agam-89/CoreSynq32/schematics/386amp.kicad_sch

## KiCad design schematics/386amp.kicad_sch (2026-04-13)

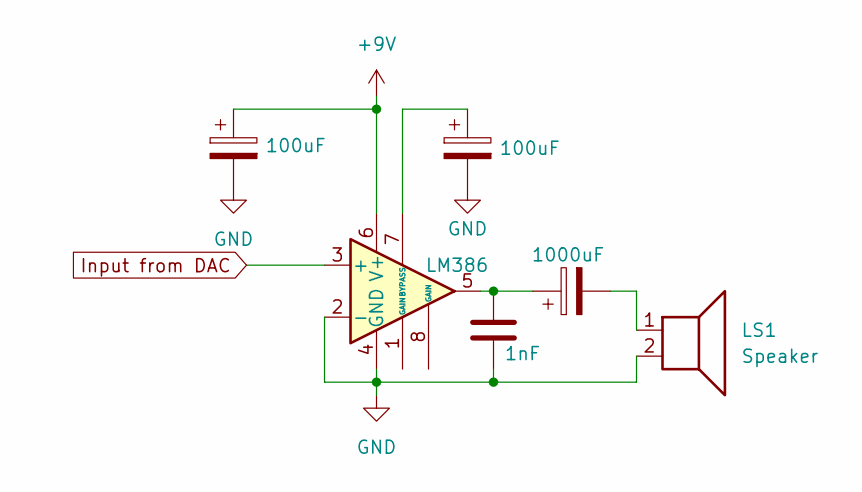
[picture p2: schematic 386amp.kicad_sch]

Parts:
100uF: C_Polarized
1000uF: 100u
C1: 1nF
LS1: Speaker
U1: LM386

Connections:
+9V: 100uF.1, U1.6 (V+)
GND: 100uF.2, C1.2, LS1.2, U1.2 (-), U1.4 (GND)
Input from DAC: U1.3 (+)
unnamed: 100uF.1, U1.7 (BYPASS)
unnamed: 1000uF.1, C1.1, U1.5
unnamed: 1000uF.2, LS1.1
