agam-89/CoreSynq32/drum_mchn/samples.h

#ifndef SAMPLES_H
#define SAMPLES_H

const uint8_t kick[] = {
127,128,127,128,127,128,127,128,128,130,134,137,131,117,121,159,214,234,214,101,12,15,22,58,124,186,198,187,154,107,87,92,120,155,168,166,153,129,111,110,121,137,148,148,141,129,121,118,124,131,136,136,141,155,174,181,175,137,79,53,46,57,78,106,122,109,87,73,70,74,84,98,108,109,103,97,95,98,106,115,123,127,128,127,126,128,133,140,143,138,121,104,99,115,157,189,203,207,200,189,177,173,176,183,188,190,187,182,176,173,172,172,173,173,171,168,164,160,158,156,154,152,149,145,140,135,131,127,123,123,127,133,138,135,116,86,67,59,56,59,64,70,72,70,67,64,63,65,68,71,73,74,74,74,75,76,79,81,83,85,87,88,90,92,94,97,100,103,106,109,112,115,119,123,125,124,121,118,119,128,147,168,180,186,187,185,181,178,177,179,181,182,182,180,178,175,173,172,172,171,170,168,166,163,160,157,155,152,149,145,140,135,129,124,119,114,110,106,102,99,96,94,93,92,92,92,94,96,98,96,92,87,83,79,76,76,77,79,82,83,84,84,85,86,87,89,92,95,98,100,103,106,110,115,121,127,133,139,145,151,156,161,166,170,173,176,178,179,181,182,183,184,184,185,185,185,185,185,185,184,184,183,182,180,178,177,177,178,179,180,180,180,180,178,177,176,174,173,171,170,169,167,165,163,161,158,155,152,149,145,141,136,131,125,118,111,103,97,90,85,80,76,72,70,67,66,64,63,62,61,60,59,59,58,58,58,59,59,59,60,61,62,63,64,66,67,69,70,72,74,75,75,75,76,77,78,79,80,81,82,83,85,88,90,93,95,98,101,104,108,113,119,125,131,138,145,152,159,165,171,176,180,184,187,189,191,193,194,195,197,197,198,199,199,199,200,200,199,199,198,198,197,196,195,193,192,191,190,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

};
const int kick_len = 5978;

const uint8_t snare[] = {
141,118,121,139,132,174,159,183,156,163,162,165,145,125,172,146,153,112,139,88,104,138,85,67,83,114,87,69,70,91,101,79,90,104,76,105,109,144,121,110,146,120,147,167,178,190,170,196,185,189,217,198,210,209,212,214,221,219,211,229,225,226,211,201,214,199,203,198,201,192,180,166,146,152,148,140,131,118,97,93,89,86,67,77,55,44,52,40,38,31,45,36,36,19,32,29,27,23,26,37,24,34,28,27,37,33,37,41,47,47,48,60,56,70,65,78,71,93,87,107,112,99,133,118,144,141,165,149,161,170,175,188,168,194,184,178,187,190,189,185,196,193,188,187,186,187,181,190,178,177,176,178,171,161,163,164,154,152,150,133,140,129,132,125,104,112,114,101,102,109,104,96,102,102,84,96,93,99,105,92,97,98,106,102,109,102,118,119,113,133,123,122,128,148,141,146,156,153,154,157,166,165,168,171,178,174,181,180,164,180,184,179,179,179,183,180,171,183,182,175,178,167,174,169,171,167,159,167,163,145,144,151,145,147,135,131,124,136,132,110,120,118,112,111,98,106,115,101,101,106,105,100,104,104,94,97,100,113,110,98,100,113,119,112,114,127,117,118,132,124,138,134,142,138,141,138,142,157,146,149,155,160,148,160,160,160,161,154,161,162,152,159,157,146,163,151,151,156,142,144,153,143,133,145,141,123,141,135,119,126,122,135,113,110,117,102,106,114,115,104,102,99,100,105,99,97,101,102,106,103,101,99,99,97,103,107,107,106,106,112,113,104,111,123,117,122,119,128,127,124,129,130,127,134,136,127,140,131,144,137,132,144,138,140,133,139,133,135,135,141,141,129,134,129,122,125,134,129,123,126,117,119,119,117,122,118,104,111,118,111,107,107,108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
};
const int snare_len = 3658;

const uint8_t hihat[] = {
136,116,139,110,155,143,74,165,106,109,180,94,137,152,108,155,88,120,150,119,140,140,115,135,126,127,116,151,125,115,146,114,149,85,136,145,108,130,131,126,146,89,127,154,97,143,131,124,133,136,120,132,97,140,141,124,126,148,117,116,136,101,172,116,108,137,125,130,121,133,134,127,122,128,156,110,118,139,112,146,122,144,124,110,125,103,158,134,118,133,111,126,134,128,131,131,127,118,143,131,110,123,135,147,105,138,121,134,136,126,107,126,161,100,151,127,117,124,128,117,141,134,121,121,123,157,95,157,109,115,132,115,156,106,131,132,122,138,125,125,124,126,131,124,145,121,120,129,137,117,131,121,127,133,120,142,120,137,118,128,129,115,141,135,123,125,123,125,126,119,148,127,131,135,89,147,119,120,134,142,117,116,146,105,151,127,112,136,124,133,124,121,141,112,127,141,134,129,112,119,139,125,131,125,123,147,120,114,136,124,123,150,100,132,135,131,114,132,120,126,157,115,139,108,125,130,133,113,138,135,129,114,128,122,115,152,110,134,136,126,120,133,121,135,125,117,137,128,118,132,139,111,127,121,129,135,128,150,104,123,132,114,147,121,119,151,130,113,125,112,152,117,123,139,126,136,125,120,101,160,123,126,137,112,141,126,109,131,124,121,142,135,132,109,125,131,126,134,129,125,124,131,139,125,112,122,137,125,137,131,116,137,132,108,154,123,109,144,102,141,128,142,122,124,109,138,151,97,141,124,129,122,132,130,139,119,118,139,124,128,121,140,117,119,138,125,138,117,129,125,138,126,103,145,117,142,119,131,126,122,146,121,114,129,132,116,154,111,131,123,126,126,135,133,116,137,107,15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
,108,101,115,47,0,73,67,82,68,14,0,0,0,79,99,116,111,98,101,114,32,50,48,49,52,0,0,73,71,78,82,14,0,0,0,83,111,117,110,100,32,76,105,98,114,97,114,121,0,105,100,51,32,150,0,0,0,73,68,51,3,0,0,0,0,1,12,84,65,76,66,0,0,0,16,0,0,0,57,57,32,68,114,117,109,32,83,97,109,112,108,101,115,84,68,82,67,0,0,0,13,0,0,0,79,99,116,111,98,101,114,32,50,48,49,52,84,80,69,49,0,0,0,9,0,0,0,57,57,83,111,117,110,100,115,67,79,77,77,0,0,0,38,0,0,0,0,0,0,0,104,116,116,112,58,47,47,57,57,115,111,117,110,100,115,46,111,114,103,47,100,114,117,109,45,115,97,109,112,108,101,115,47,84,67,79,78,0,0,0,14,0,0,0,83,111,117,110,100,32,76,105,98,114,97,114,121
};
const int hihat_len = 3978;

#endif
